FASTSHIFT/X-TRACK/ArtDesign/地图示例.png

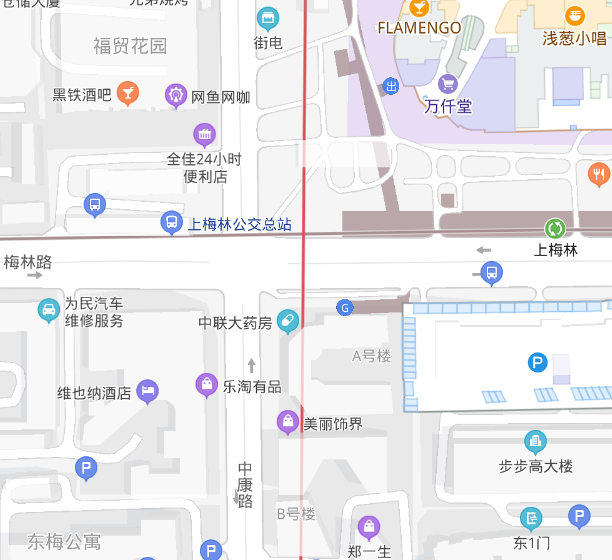
ArtDesign/地图示例.png
