FASTSHIFT/X-TRACK/Images/骑行测试.jpg

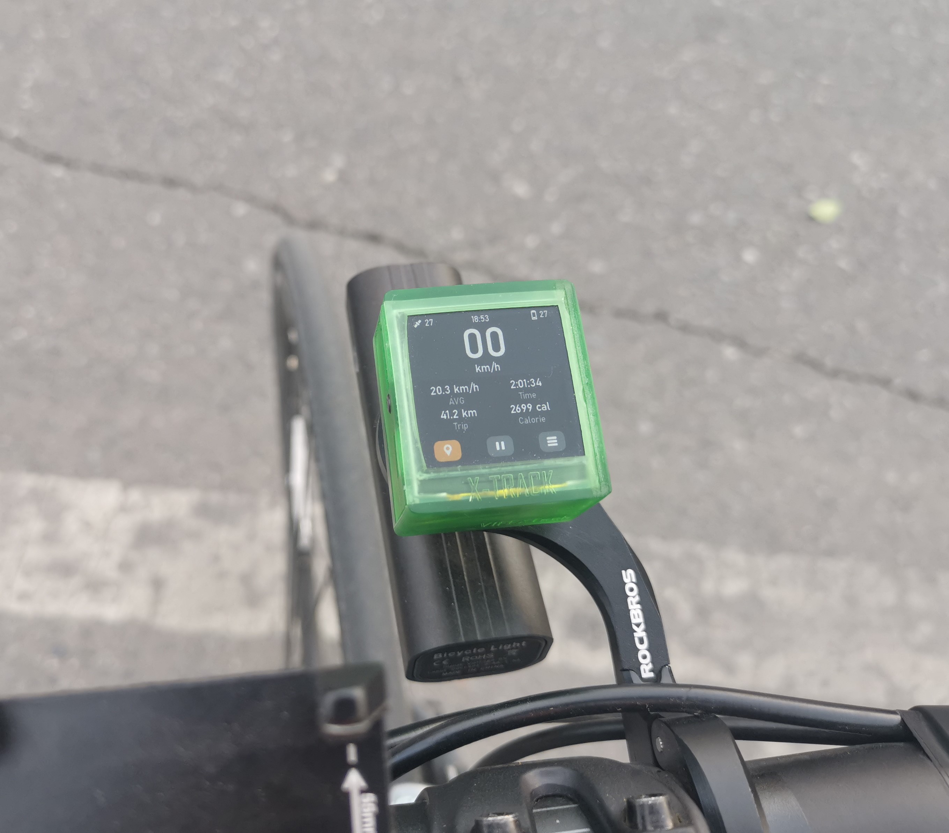
Images/骑行测试.jpg
