FASTSHIFT/X-TRACK/Tools/Images/fileconv.PNG

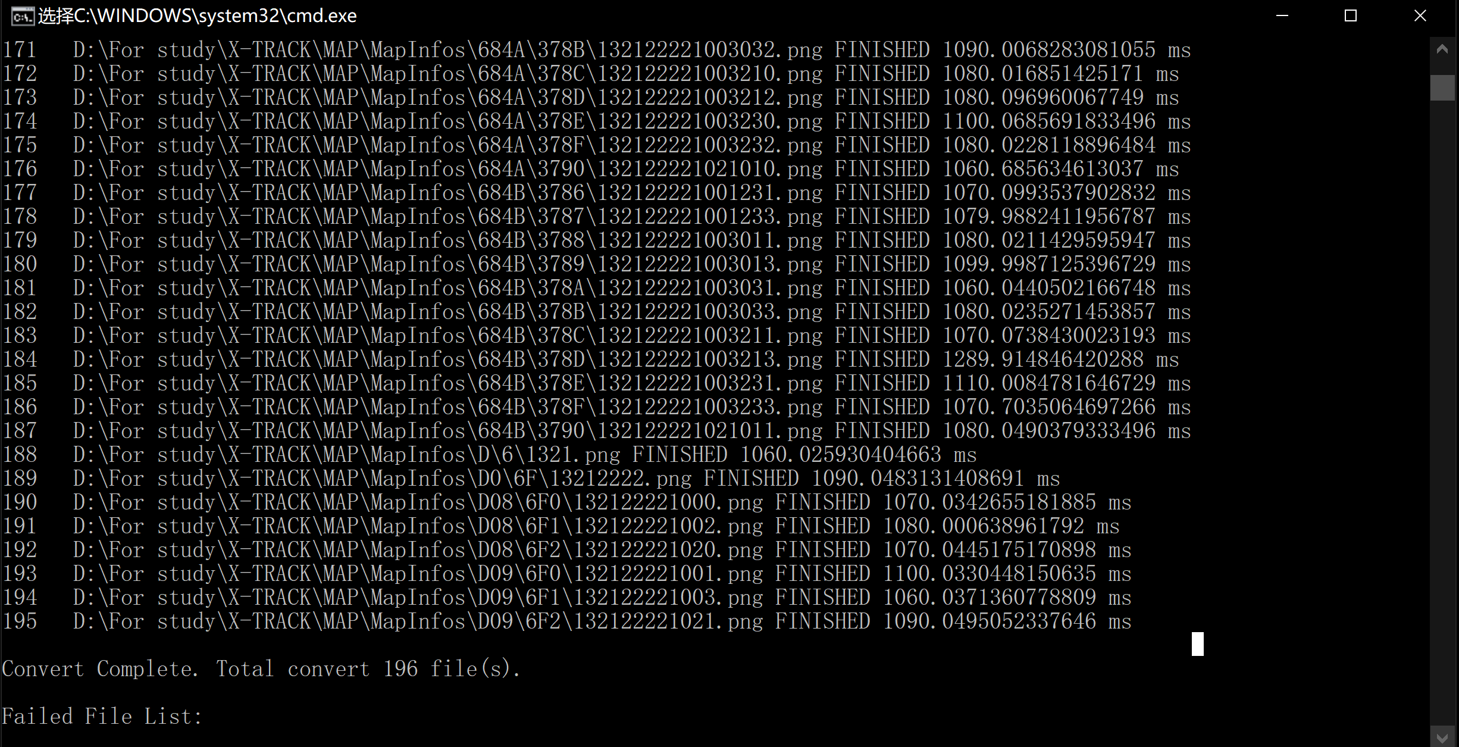
Tools/Images/fileconv.PNG
