FASTSHIFT/X-TRACK/Tools/Images/filerename.PNG

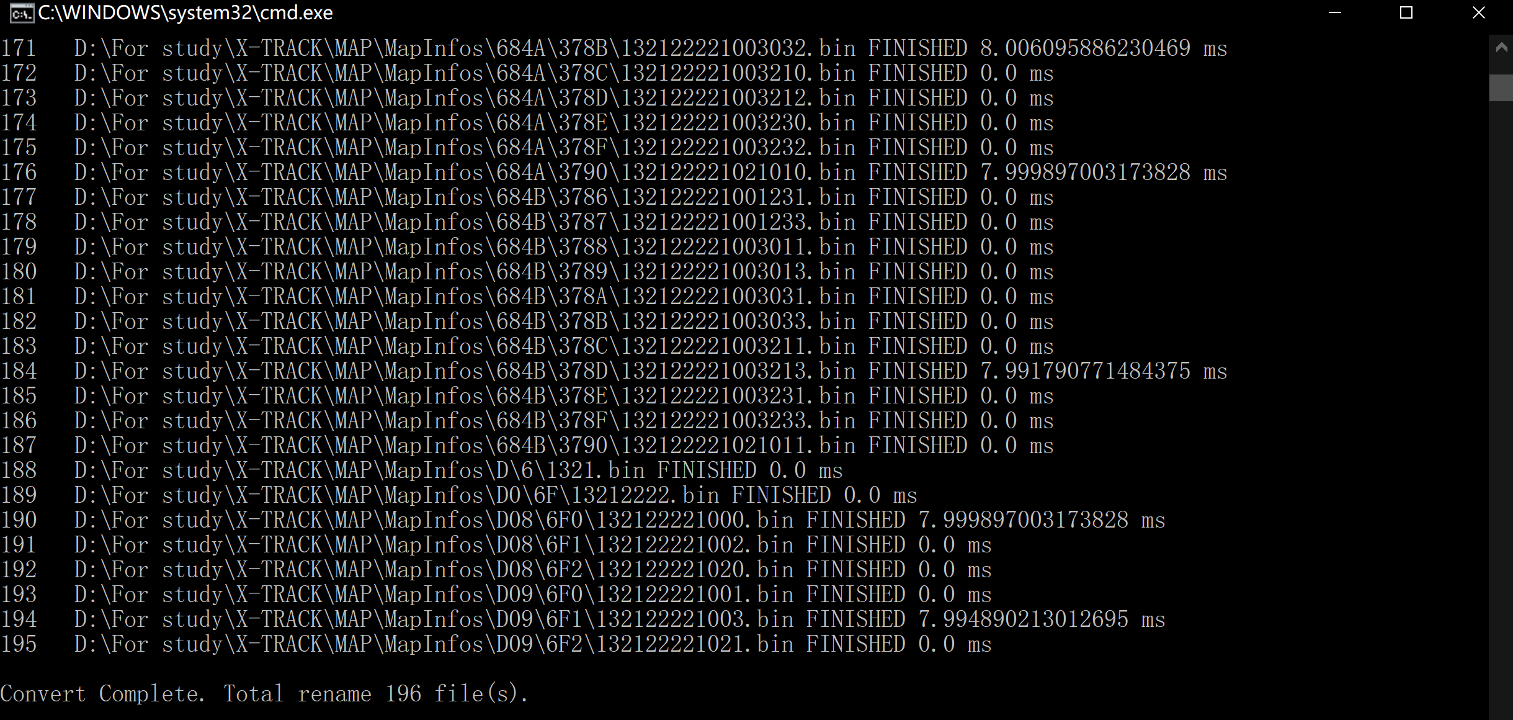
Tools/Images/filerename.PNG
