FASTSHIFT/X-TRACK/Software/X-Track/MDK-ARM_F403A/Platform/Core/adc.c

/*
 * MIT License
 * Copyright (c) 2017 - 2022 _VIFEXTech
 *
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
 * THE SOFTWARE IS PROVIDED "AS IS", WITHOUT WARRANTY OF ANY KIND, EXPRESS OR
 * IMPLIED, INCLUDING BUT NOT LIMITED TO THE WARRANTIES OF MERCHANTABILITY,
 * FITNESS FOR A PARTICULAR PURPOSE AND NONINFRINGEMENT. IN NO EVENT SHALL THE
 * AUTHORS OR COPYRIGHT HOLDERS BE LIABLE FOR ANY CLAIM, DAMAGES OR OTHER
 * LIABILITY, WHETHER IN AN ACTION OF CONTRACT, TORT OR OTHERWISE, ARISING FROM,
 * OUT OF OR IN CONNECTION WITH THE SOFTWARE OR THE USE OR OTHER DEALINGS IN THE
 * SOFTWARE.
 */
#include "adc.h"
#include <stdbool.h>

#define ADC_DMA_REGMAX 18

/*引脚注册个数*/
static uint8_t ADC_DMA_RegCnt = 0;

/*ADC通道注册列表*/
static uint8_t ADC_DMA_RegChannelList[ADC_DMA_REGMAX] = {0};

/*ADC DMA缓存数组*/
static uint16_t ADC_DMA_ConvertedValue[ADC_DMA_REGMAX] = {0};

/**
  * @brief  搜索注册列表，找出ADC通道对应的索引号
  * @param  ADC_Channel:ADC通道号
  * @retval ADC通道注册列表对应索引号，-1:未找到对应通道号
  */
static int16_t ADC_DMA_SearchChannel(uint16_t ADC_Channel)
{
    uint8_t index;

    for(index = 0; index < ADC_DMA_RegCnt; index++)
    {
        if(ADC_Channel == ADC_DMA_RegChannelList[index])
        {
            return index;
        }
    }
    return -1;
}

/**
  * @brief  ADC 配置
  * @param  ADCx: ADC地址
  * @retval 无
  */
void ADCx_Init(ADC_Type* ADCx)
{
    ADC_InitType ADC_InitStructure;

    if(ADCx == ADC1)
    {
        RCC_APB2PeriphClockCmd(RCC_APB2PERIPH_ADC1, ENABLE);
    }
    else if(ADCx == ADC2)
    {
        RCC_APB2PeriphClockCmd(RCC_APB2PERIPH_ADC2, ENABLE);
    }
#ifdef ADC3
    else if(ADCx == ADC3)
    {
        RCC_APB2PeriphClockCmd(RCC_APB2PERIPH_ADC3, ENABLE);
    }
#endif
    else
    {
        return;
    }

    RCC_ADCCLKConfig(RCC_APB2CLK_Div8);

    ADC_Reset(ADCx);
    ADC_StructInit(&ADC_InitStructure);
    ADC_InitStructure.ADC_Mode = ADC_Mode_Independent;
    ADC_InitStructure.ADC_ScanMode = DISABLE;
    ADC_InitStructure.ADC_ContinuousMode = DISABLE;
    ADC_InitStructure.ADC_ExternalTrig = ADC_ExternalTrig_None;
    ADC_InitStructure.ADC_DataAlign = ADC_DataAlign_Right;
    ADC_InitStructure.ADC_NumOfChannel = 1;
    ADC_Init(ADCx, &ADC_InitStructure);

    ADC_Ctrl(ADCx, ENABLE);
    ADC_RstCalibration(ADCx);
    while(ADC_GetResetCalibrationStatus(ADCx));
    ADC_StartCalibration(ADCx);
    while(ADC_GetCalibrationStatus(ADCx));
}

/**
  * @brief  获取 ADC 值
  * @param  ADCx: ADC地址
  * @param  ADC_Channel: ADC通道
  * @retval 无
  */
uint16_t ADCx_GetValue(ADC_Type* ADCx, uint16_t ADC_Channel)
{
    ADC_RegularChannelConfig(ADCx, ADC_Channel, 1, ADC_SampleTime_41_5);

    ADC_SoftwareStartConvCtrl(ADCx, ENABLE);
    while(!ADC_GetFlagStatus(ADCx, ADC_FLAG_EC));
    return ADC_GetConversionValue(ADCx);
}

/**
  * @brief  注册需要DMA搬运的ADC通道
  * @param  ADC_Channel:ADC通道号
  * @retval 见ADC_DMA_Res_Type
  */
ADC_DMA_Res_Type ADC_DMA_Register(uint8_t ADC_Channel)
{
    /*初始化ADC通道列表*/
    static bool isInit = false;
    if(!isInit)
    {
        uint8_t i;
        for(i = 0; i < ADC_DMA_REGMAX; i++)
        {
            ADC_DMA_RegChannelList[i] = 0xFF;
        }
        isInit = true;
    }

    /*是否是合法ADC通道*/
    if(!IS_ADC_CHANNEL(ADC_Channel))
        return ADC_DMA_RES_NOT_ADC_CHANNEL;

    /*是否已在引脚列表重复注册*/
    if(ADC_DMA_SearchChannel(ADC_Channel) != -1)
        return ADC_DMA_RES_DUPLICATE_REGISTRATION;

    /*是否超出最大注册个数*/
    if(ADC_DMA_RegCnt >= ADC_DMA_REGMAX)
        return ADC_DMA_RES_MAX_NUM_OF_REGISTRATIONS_EXCEEDED;

    /*写入注册列表*/
    ADC_DMA_RegChannelList[ADC_DMA_RegCnt] = ADC_Channel;

    /*注册个数+1*/
    ADC_DMA_RegCnt++;

    return ADC_DMA_RES_OK;
}

/**
  * @brief  获取已注册的ADC DMA通道数量
  * @param  无
  * @retval ADC DMA通道数量
  */
uint8_t ADC_DMA_GetRegisterCount(void)
{
    return ADC_DMA_RegCnt;
}

/**
  * @brief  ADC DMA 配置
  * @param  无
  * @retval 无
  */
void ADC_DMA_Init(void)
{
    DMA_InitType DMA_InitStructure;
    ADC_InitType ADC_InitStructure;
    uint8_t index;

    RCC_AHBPeriphClockCmd(RCC_AHBPERIPH_DMA1, ENABLE);
    RCC_APB2PeriphClockCmd(RCC_APB2PERIPH_ADC1, ENABLE);

    DMA_Reset(DMA1_Channel1);

    DMA_DefaultInitParaConfig(&DMA_InitStructure);
    DMA_InitStructure.DMA_PeripheralBaseAddr = (uint32_t) (&(ADC1->RDOR));
    DMA_InitStructure.DMA_MemoryBaseAddr = (uint32_t)ADC_DMA_ConvertedValue;
    DMA_InitStructure.DMA_Direction = DMA_DIR_PERIPHERALSRC;
    DMA_InitStructure.DMA_BufferSize = ADC_DMA_RegCnt;
    DMA_InitStructure.DMA_PeripheralInc = DMA_PERIPHERALINC_DISABLE;
    DMA_InitStructure.DMA_MemoryInc = DMA_MEMORYINC_ENABLE;
    DMA_InitStructure.DMA_PeripheralDataWidth = DMA_PERIPHERALDATAWIDTH_HALFWORD;
    DMA_InitStructure.DMA_MemoryDataWidth = DMA_MEMORYDATAWIDTH_HALFWORD;
    DMA_InitStructure.DMA_Mode = DMA_MODE_CIRCULAR;
    DMA_InitStructure.DMA_Priority = DMA_PRIORITY_HIGH;
    DMA_InitStructure.DMA_MTOM = DMA_MEMTOMEM_DISABLE;
    DMA_Init(DMA1_Channel1, &DMA_InitStructure);

    DMA_ChannelEnable(DMA1_Channel1, ENABLE);

    ADC_Reset(ADC1);

    ADC_StructInit(&ADC_InitStructure);
    ADC_InitStructure.ADC_Mode = ADC_Mode_Independent;
    ADC_InitStructure.ADC_ScanMode = ENABLE;
    ADC_InitStructure.ADC_ContinuousMode = ENABLE;
    ADC_InitStructure.ADC_ExternalTrig = ADC_ExternalTrig_None;
    ADC_InitStructure.ADC_DataAlign = ADC_DataAlign_Right;
    ADC_InitStructure.ADC_NumOfChannel = ADC_DMA_RegCnt;
    ADC_Init(ADC1, &ADC_InitStructure);

    RCC_ADCCLKConfig(RCC_APB2CLK_Div8);

    for(index = 0; index < ADC_DMA_RegCnt; index++)
    {
        ADC_RegularChannelConfig(
            ADC1,
            ADC_DMA_RegChannelList[index],
            index + 1,
            ADC_SampleTime_55_5
        );

        if(ADC_DMA_RegChannelList[index] == ADC_Channel_TempSensor)
        {
            ADC_TempSensorVrefintCtrl(ENABLE);
        }
    }

    ADC_DMACtrl(ADC1, ENABLE);

    ADC_Ctrl(ADC1, ENABLE);

    ADC_RstCalibration(ADC1);

    while(ADC_GetResetCalibrationStatus(ADC1));

    ADC_StartCalibration(ADC1);
    while(ADC_GetCalibrationStatus(ADC1));

    ADC_SoftwareStartConvCtrl(ADC1, ENABLE);
}

/**
  * @brief  获取DMA搬运的ADC值
  * @param  ADC_Channel:ADC通道号
  * @retval ADC值
  */
uint16_t ADC_DMA_GetValue(uint8_t ADC_Channel)
{
    int16_t index;

    if(!IS_ADC_CHANNEL(ADC_Channel))
        return 0;

    index = ADC_DMA_SearchChannel(ADC_Channel);
    if(index == -1)
        return 0;

    return ADC_DMA_ConvertedValue[index];
}
