FASTSHIFT/X-TRACK/Software/X-Track/MDK-ARM_F403A/Platform/Core/exti.c

/*
 * MIT License
 * Copyright (c) 2017 - 2022 _VIFEXTech
 *
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
 * THE SOFTWARE IS PROVIDED "AS IS", WITHOUT WARRANTY OF ANY KIND, EXPRESS OR
 * IMPLIED, INCLUDING BUT NOT LIMITED TO THE WARRANTIES OF MERCHANTABILITY,
 * FITNESS FOR A PARTICULAR PURPOSE AND NONINFRINGEMENT. IN NO EVENT SHALL THE
 * AUTHORS OR COPYRIGHT HOLDERS BE LIABLE FOR ANY CLAIM, DAMAGES OR OTHER
 * LIABILITY, WHETHER IN AN ACTION OF CONTRACT, TORT OR OTHERWISE, ARISING FROM,
 * OUT OF OR IN CONNECTION WITH THE SOFTWARE OR THE USE OR OTHER DEALINGS IN THE
 * SOFTWARE.
 */
#include "exti.h"
#include "gpio.h"

#define EXTI_GetPortSourceGPIOx(Pin) GPIO_GetPortNum(Pin)
#define EXTI_GetPinSourcex(Pin)      GPIO_GetPinNum(Pin)

static EXTI_CallbackFunction_t EXTI_Function[16] = {0};

/**
  * @brief  获取外部中断的中断通道
  * @param  Pin: 引脚编号
  * @retval 通道编号
  */
static IRQn_Type EXTI_GetIRQn(uint8_t Pin)
{
    IRQn_Type EXTIx_IRQn = EXTI0_IRQn;
    uint8_t Pinx = GPIO_GetPinNum(Pin);

    if(Pinx <= 4)
    {
        switch(Pinx)
        {
        case 0:
            EXTIx_IRQn = EXTI0_IRQn;
            break;
        case 1:
            EXTIx_IRQn = EXTI1_IRQn;
            break;
        case 2:
            EXTIx_IRQn = EXTI2_IRQn;
            break;
        case 3:
            EXTIx_IRQn = EXTI3_IRQn;
            break;
        case 4:
            EXTIx_IRQn = EXTI4_IRQn;
            break;
        }
    }
    else if(Pinx >= 5 && Pinx <= 9)
    {
        EXTIx_IRQn = EXTI9_5_IRQn;
    }
    else if(Pinx >= 10 && Pinx <= 15)
    {
        EXTIx_IRQn = EXTI15_10_IRQn;
    }

    return EXTIx_IRQn;
}

/**
  * @brief  外部中断初始化
  * @param  Pin: 引脚编号
  * @param  Function: 回调函数
  * @param  Trigger_Mode: 触发方式
  * @param  PreemptionPriority: 抢占优先级
  * @param  SubPriority: 子优先级
  * @retval 无
  */
void EXTIx_Init(
    uint8_t Pin,
    EXTI_CallbackFunction_t Function,
    EXTITrigger_Type Trigger_Mode,
    uint8_t PreemptionPriority,
    uint8_t SubPriority
)
{
    EXTI_InitType EXTI_InitStructure;
    NVIC_InitType NVIC_InitStructure;
    uint8_t Pinx;

    if(!IS_PIN(Pin))
        return;

    Pinx = GPIO_GetPinNum(Pin);

    if(Pinx > 15)
        return;

    EXTI_Function[Pinx] = Function;

    RCC_APB2PeriphClockCmd(RCC_APB2PERIPH_AFIO, ENABLE);
    GPIO_EXTILineConfig(GPIO_GetPortNum(Pin), Pinx);

    EXTI_StructInit(&EXTI_InitStructure);
    EXTI_InitStructure.EXTI_Line = 1 << Pinx;
    EXTI_InitStructure.EXTI_Mode = EXTI_Mode_Interrupt;
    EXTI_InitStructure.EXTI_Trigger = Trigger_Mode;
    EXTI_InitStructure.EXTI_LineEnable = ENABLE;
    EXTI_Init(&EXTI_InitStructure);

    NVIC_InitStructure.NVIC_IRQChannel = EXTI_GetIRQn(Pin);
    NVIC_InitStructure.NVIC_IRQChannelPreemptionPriority = PreemptionPriority;
    NVIC_InitStructure.NVIC_IRQChannelSubPriority = SubPriority;
    NVIC_InitStructure.NVIC_IRQChannelCmd = ENABLE;
    NVIC_Init(&NVIC_InitStructure);
}

/**
  * @brief  外部中断初始化 (Arduino)
  * @param  Pin: 引脚编号
  * @param  function: 回调函数
  * @param  Trigger_Mode: 触发方式
  * @retval 无
  */
void attachInterrupt(uint8_t Pin, EXTI_CallbackFunction_t Function, EXTITrigger_Type Trigger_Mode)
{
    EXTIx_Init(
        Pin,
        Function,
        Trigger_Mode,
        EXTI_PREEMPTIONPRIORITY_DEFAULT,
        EXTI_SUBPRIORITY_DEFAULT
    );
}

/**
  * @brief  关闭给定的中断 (Arduino)
  * @param  Pin: 引脚编号
  * @retval 无
  */
void detachInterrupt(uint8_t Pin)
{
    if(!IS_PIN(Pin))
        return;

    NVIC_DisableIRQ(EXTI_GetIRQn(Pin));
}

#define EXTIx_IRQHANDLER(n) \
do{\
    if(EXTI_GetIntStatus(EXTI_Line##n) != RESET)\
    {\
        if(EXTI_Function[n]) EXTI_Function[n]();\
        EXTI_ClearIntPendingBit(EXTI_Line##n);\
    }\
}while(0)

/**
  * @brief  外部中断入口，通道0
  * @param  无
  * @retval 无
  */
void EXTI0_IRQHandler(void)
{
    EXTIx_IRQHANDLER(0);
}

/**
  * @brief  外部中断入口，通道1
  * @param  无
  * @retval 无
  */
void EXTI1_IRQHandler(void)
{
    EXTIx_IRQHANDLER(1);
}

/**
  * @brief  外部中断入口，通道2
  * @param  无
  * @retval 无
  */
void EXTI2_IRQHandler(void)
{
    EXTIx_IRQHANDLER(2);
}

/**
  * @brief  外部中断入口，通道3
  * @param  无
  * @retval 无
  */
void EXTI3_IRQHandler(void)
{
    EXTIx_IRQHANDLER(3);
}

/**
  * @brief  外部中断入口，通道4
  * @param  无
  * @retval 无
  */
void EXTI4_IRQHandler(void)
{
    EXTIx_IRQHANDLER(4);
}

/**
  * @brief  外部中断入口，通道9~5
  * @param  无
  * @retval 无
  */
void EXTI9_5_IRQHandler(void)
{
    EXTIx_IRQHANDLER(5);
    EXTIx_IRQHANDLER(6);
    EXTIx_IRQHANDLER(7);
    EXTIx_IRQHANDLER(8);
    EXTIx_IRQHANDLER(9);
}

/**
  * @brief  外部中断入口，通道15~10
  * @param  无
  * @retval 无
  */
void EXTI15_10_IRQHandler(void)
{
    EXTIx_IRQHANDLER(10);
    EXTIx_IRQHANDLER(11);
    EXTIx_IRQHANDLER(12);
    EXTIx_IRQHANDLER(13);
    EXTIx_IRQHANDLER(14);
    EXTIx_IRQHANDLER(15);
}
