FASTSHIFT/X-TRACK/Tools/GNSSToolKit_Lite/GNSSToolKitLite_configs.ini

[MainConfig]
MdiCnt=2
MainForm.WinState=2
MainForm.Size.Width=1024
MainForm.Size.Height=800
MainForm.Location.X=0
MainForm.Location.Y=0
MainForm.IsSizeable=True
[Config0]
ConfigName=Config0
BDPRN=200
GNPRN=64
PortName=COM3
BaudRate=115200
Parity=0
DataBits=8
StopBits=0
SaveFilePath=C:\Users\_VIFEXTech\Desktop\ATGM332D 北斗定位模块\模块配置工具\gps_save.txt
BurstCnt=500
InBuffSize=4096
TimeOut=1
OpenFilePath=
Delay=0
Update.AutoBaud=41
Update.AutoInterval=15
Update.SpiClock=0
Update.BaseID=20120715
Update.MainExe=
Evaluate.FileName=
Evaluate.PointType=0
Evaluate.Lon=N/A
Evaluate.Lat=N/A
Evaluate.Alt=N/A
SateBarHeight=100
SatePanelMask=7
IsSateVertical=True
SateInUseColor=ff0000ff
SateNotInUseColor=ff8f8f8f
SateValueColor=ff000000
IsTextPanelCollapsed=True
DataChType=0
TEXT_FORM.IsFormShow=True
TEXT_FORM.Size.Width=1190
TEXT_FORM.Size.Height=737
TEXT_FORM.Location.X=0
TEXT_FORM.Location.Y=0
TEXT_FORM.WinState=0
TEXT_FORM.ZOrder=0
PLAN_FORM.IsFormShow=False
PLAN_FORM.Size.Width=0
PLAN_FORM.Size.Height=0
PLAN_FORM.Location.X=0
PLAN_FORM.Location.Y=0
PLAN_FORM.WinState=0
PLAN_FORM.ZOrder=-1
CONS_FORM.IsFormShow=False
CONS_FORM.Size.Width=0
CONS_FORM.Size.Height=0
CONS_FORM.Location.X=0
CONS_FORM.Location.Y=0
CONS_FORM.WinState=0
CONS_FORM.ZOrder=-1
SATE_FORM.IsFormShow=False
SATE_FORM.Size.Width=0
SATE_FORM.Size.Height=0
SATE_FORM.Location.X=0
SATE_FORM.Location.Y=0
SATE_FORM.WinState=0
SATE_FORM.ZOrder=-1
TMSG_FORM.IsFormShow=True
TMSG_FORM.Size.Width=628
TMSG_FORM.Size.Height=609
TMSG_FORM.Location.X=554
TMSG_FORM.Location.Y=16
TMSG_FORM.WinState=0
TMSG_FORM.ZOrder=1
INFO_FORM.IsFormShow=False
INFO_FORM.Size.Width=0
INFO_FORM.Size.Height=0
INFO_FORM.Location.X=0
INFO_FORM.Location.Y=0
INFO_FORM.WinState=0
INFO_FORM.ZOrder=-1
[Config1]
ConfigName=Config1
BDPRN=200
GNPRN=64
PortName=COM1
BaudRate=9600
Parity=0
DataBits=8
StopBits=0
SaveFilePath=C:\Users\_VIFEXTech\Desktop\ATGM332D 北斗定位模块\模块配置工具\gps_save.txt
BurstCnt=500
InBuffSize=4096
TimeOut=1
OpenFilePath=
Delay=0
Update.AutoBaud=41
Update.AutoInterval=15
Update.SpiClock=0
Update.BaseID=20120715
Update.MainExe=
Evaluate.FileName=
Evaluate.PointType=0
Evaluate.Lon=N/A
Evaluate.Lat=N/A
Evaluate.Alt=N/A
SateBarHeight=100
SatePanelMask=7
IsSateVertical=True
SateInUseColor=ff0000ff
SateNotInUseColor=ff8f8f8f
SateValueColor=ff000000
IsTextPanelCollapsed=True
DataChType=0
TEXT_FORM.IsFormShow=False
TEXT_FORM.Size.Width=0
TEXT_FORM.Size.Height=0
TEXT_FORM.Location.X=0
TEXT_FORM.Location.Y=0
TEXT_FORM.WinState=0
TEXT_FORM.ZOrder=-1
PLAN_FORM.IsFormShow=False
PLAN_FORM.Size.Width=0
PLAN_FORM.Size.Height=0
PLAN_FORM.Location.X=0
PLAN_FORM.Location.Y=0
PLAN_FORM.WinState=0
PLAN_FORM.ZOrder=-1
CONS_FORM.IsFormShow=False
CONS_FORM.Size.Width=0
CONS_FORM.Size.Height=0
CONS_FORM.Location.X=0
CONS_FORM.Location.Y=0
CONS_FORM.WinState=0
CONS_FORM.ZOrder=-1
SATE_FORM.IsFormShow=False
SATE_FORM.Size.Width=0
SATE_FORM.Size.Height=0
SATE_FORM.Location.X=0
SATE_FORM.Location.Y=0
SATE_FORM.WinState=0
SATE_FORM.ZOrder=-1
TMSG_FORM.IsFormShow=False
TMSG_FORM.Size.Width=0
TMSG_FORM.Size.Height=0
TMSG_FORM.Location.X=0
TMSG_FORM.Location.Y=0
TMSG_FORM.WinState=0
TMSG_FORM.ZOrder=-1
INFO_FORM.IsFormShow=False
INFO_FORM.Size.Width=0
INFO_FORM.Size.Height=0
INFO_FORM.Location.X=0
INFO_FORM.Location.Y=0
INFO_FORM.WinState=0
INFO_FORM.ZOrder=-1
