FASTSHIFT/X-TRACK/Software/X-Track/Simulator/LVGL.Simulator/resource.h

//{{NO_DEPENDENCIES}}
// Microsoft Visual C++ 生成的包含文件。
// 供 LVGL.Simulator.rc 使用
//
#define IDI_LVGL                       101

// Next default values for new objects
//
#ifdef APSTUDIO_INVOKED
#ifndef APSTUDIO_READONLY_SYMBOLS
#define _APS_NEXT_RESOURCE_VALUE        102
#define _APS_NEXT_COMMAND_VALUE         40001
#define _APS_NEXT_CONTROL_VALUE         1001
#define _APS_NEXT_SYMED_VALUE           101
#endif
#endif
